kasbah/push-on-hold-off/simulation/push-on-hold-off.asc

C1: cap; 10µF
C2: cap; 1µF
C3: cap; 0.1µF
D1: diode; 1N4148
M1: nmos; IRF7309N
M2: pmos; IRF7309P
R1: res; 10k
R2: res; 100k
R3: res; 300k
R4: res; 100k
R5: res; 100Meg
S1: sw
V1: voltage; PULSE(0 3.3)
V2: voltage; PWL(0 -1 0.4 -1 0.400001 1 0.5 1 0.500001 -1 1 -1 1.00001 1 2 1 2.00001 -1 8 -1 8.0001 1 15 1 15.0001 -1 21 -1 21.0001 1 22 1 22.0001 -1 26 -1 26.0001 1 27 1 27.001 -1)
Named nets: 0, Vout, Vin, Vswitch
.tran 30
http://www.mosaic-industries.com/embedded-systems/microcontroller-projects/electronic-circuits/push-button-switch-turn-on/latching-toggle-power-switch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
.model SW SW()
